8BitMixtape/8Bit_EuroRack-7hp/frontplate/.svg2shenzhen-cache/images/F.Silk_g9833.png

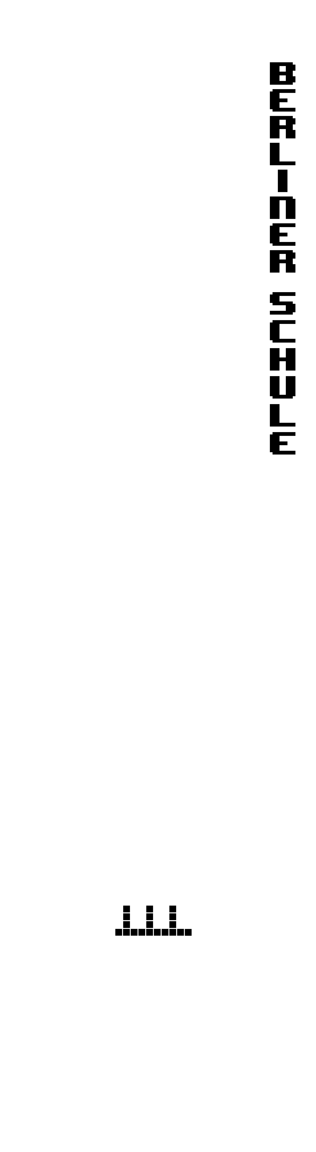
frontplate/.svg2shenzhen-cache/images/F.Silk_g9833.png
