8BitMixtape/8Bit_EuroRack-7hp/photos/8bit_Eurorack_layout_7hp_v03.png

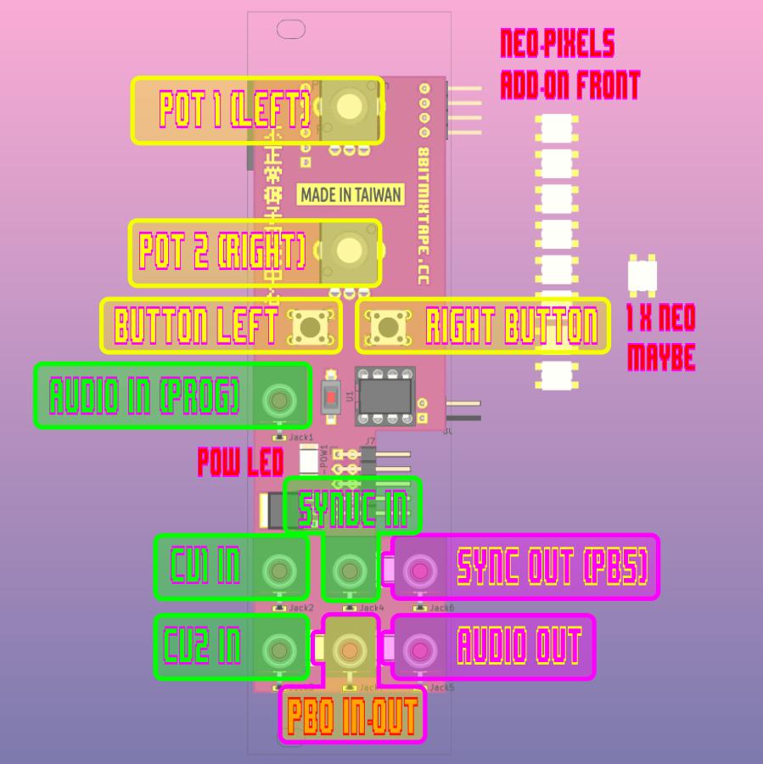
photos/8bit_Eurorack_layout_7hp_v03.png
