8BitMixtape/8Bit_EuroRack-7hp/photos/2083851114_8UBFDOnC_PJ-341.jpg

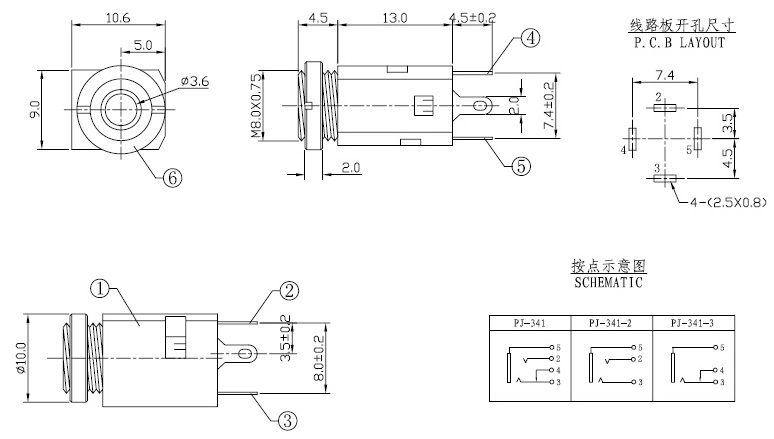
photos/2083851114_8UBFDOnC_PJ-341.jpg
