8BitMixtape/8Bit_EuroRack-7hp/photos/6369300611783734718454818.jpg

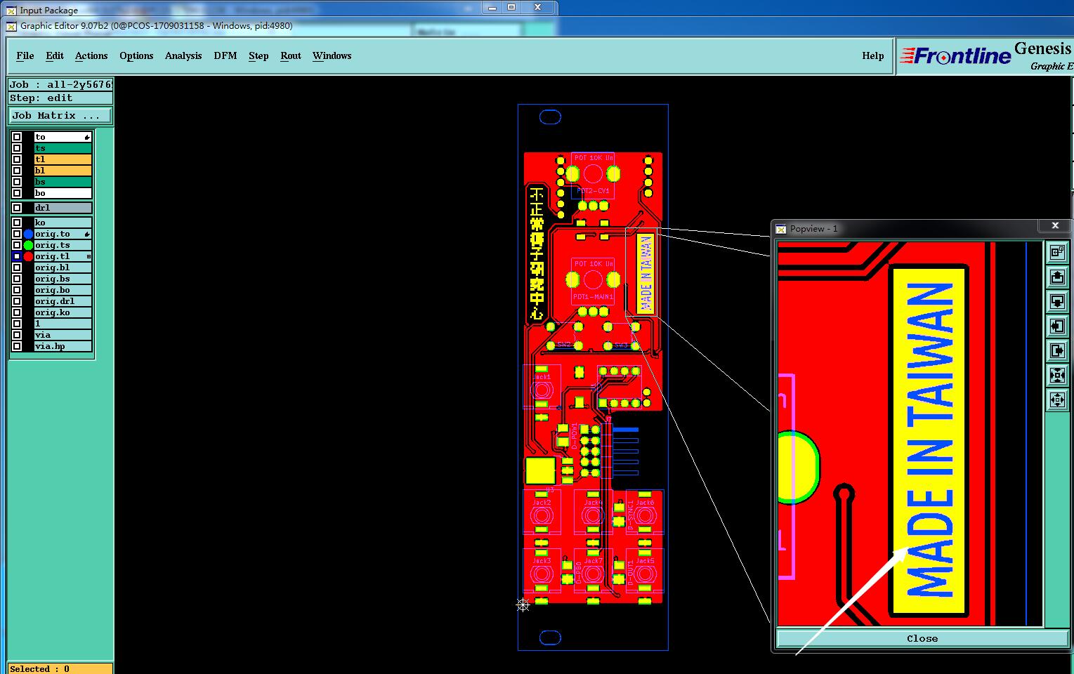
photos/6369300611783734718454818.jpg
