8BitMixtape/8Bit_EuroRack-7hp/photos/IMG_20190508_230714.jpg

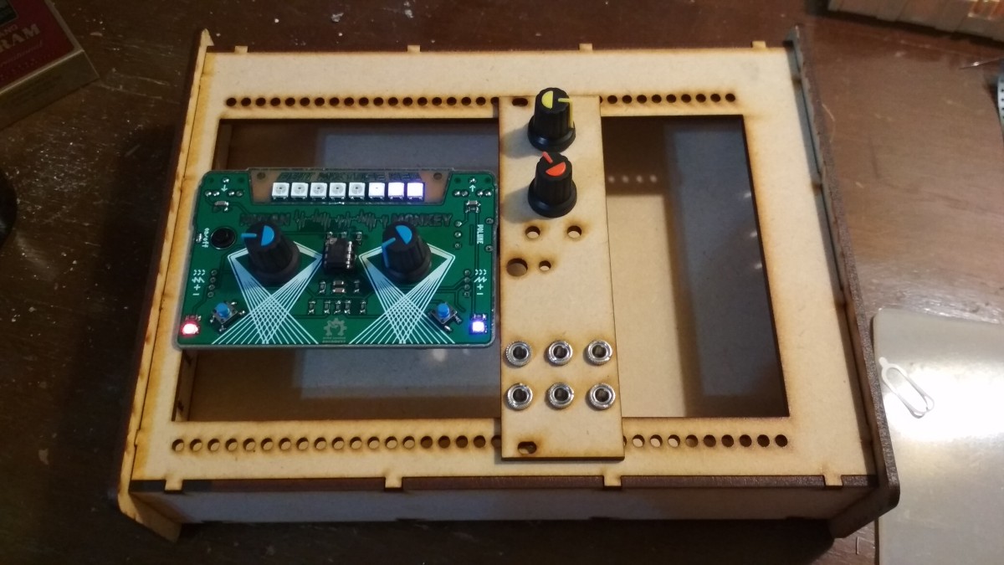
photos/IMG_20190508_230714.jpg
