8BitMixtape/8Bit_EuroRack-7hp/photos/IMG_20190508_235629.jpg

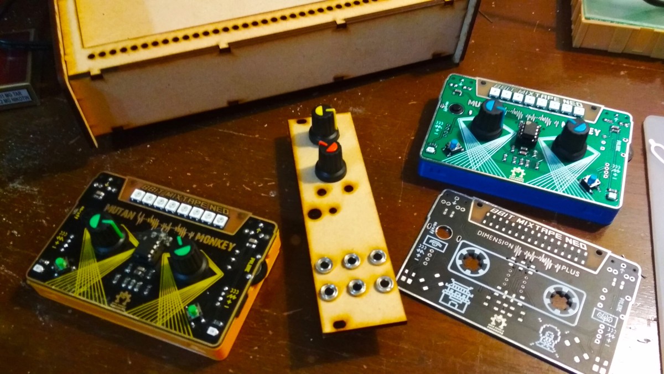
photos/IMG_20190508_235629.jpg
