8BitMixtape/8Bit_EuroRack-7hp/photos/IMG_20190514_142404.jpg

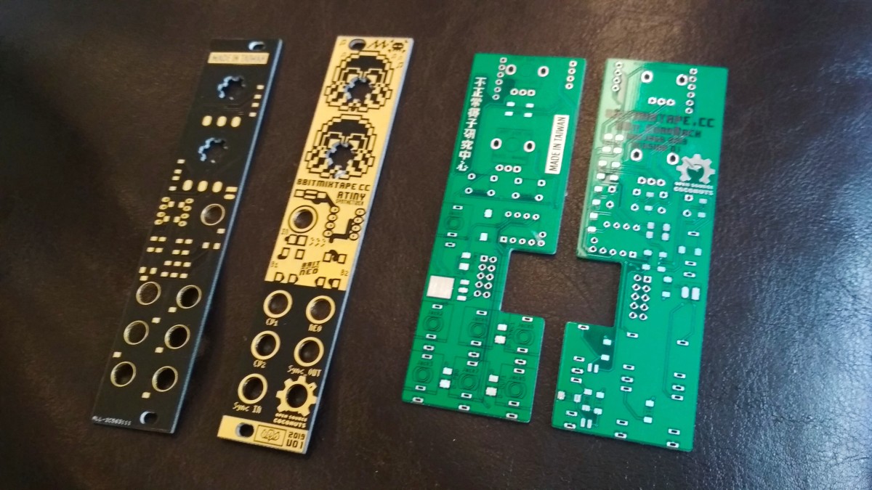
photos/IMG_20190514_142404.jpg
