8BitMixtape/8Bit_EuroRack-7hp/photos/IMG_20190514_191359.jpg

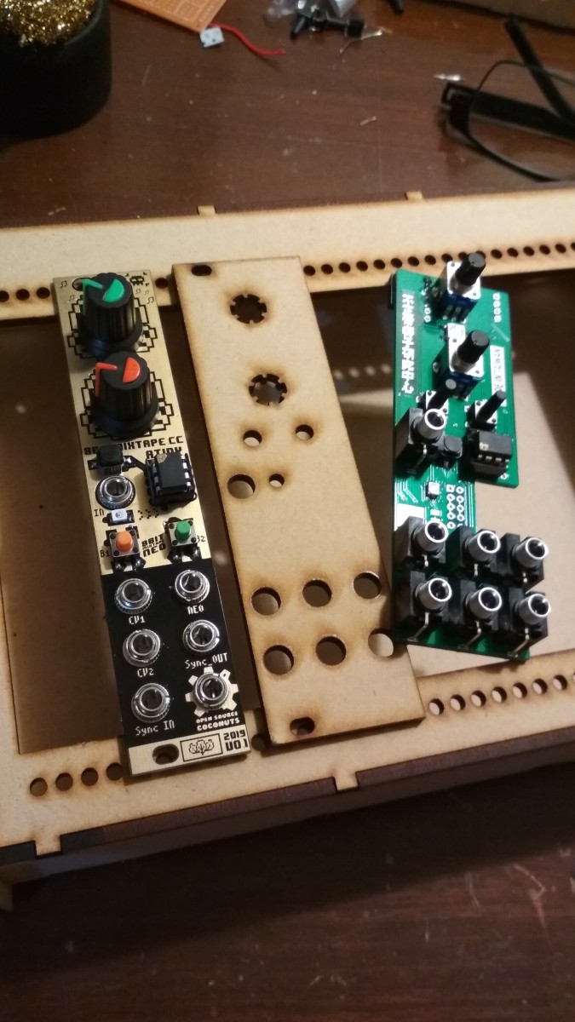
photos/IMG_20190514_191359.jpg
