8BitMixtape/8Bit_EuroRack-7hp/photos/Mixtape_goes_Modular_firstPrototype.jpg

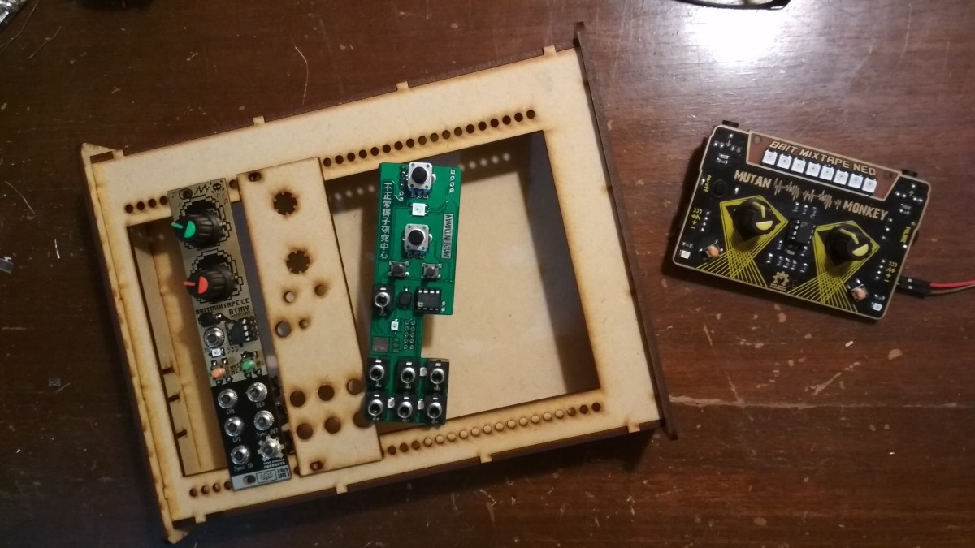
photos/Mixtape_goes_Modular_firstPrototype.jpg
