8BitMixtape/8Bit_EuroRack-7hp/photos/parts_height.png

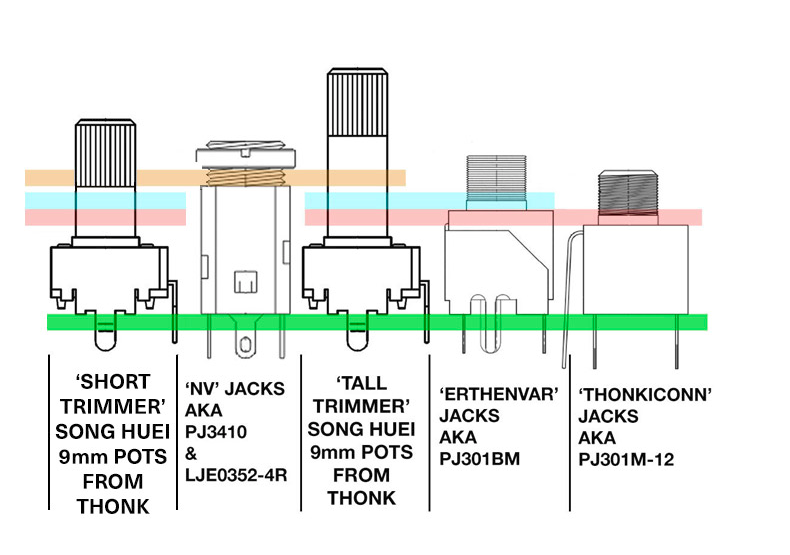
photos/parts_height.png
